jbrazio/ardufocus/.pages/assets/images/misc/homer.png

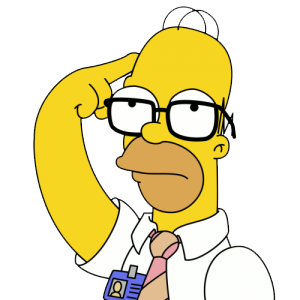
.pages/assets/images/misc/homer.png
