jbrazio/ardufocus/.pages/assets/images/pages/28byj-48-uln2003.jpg

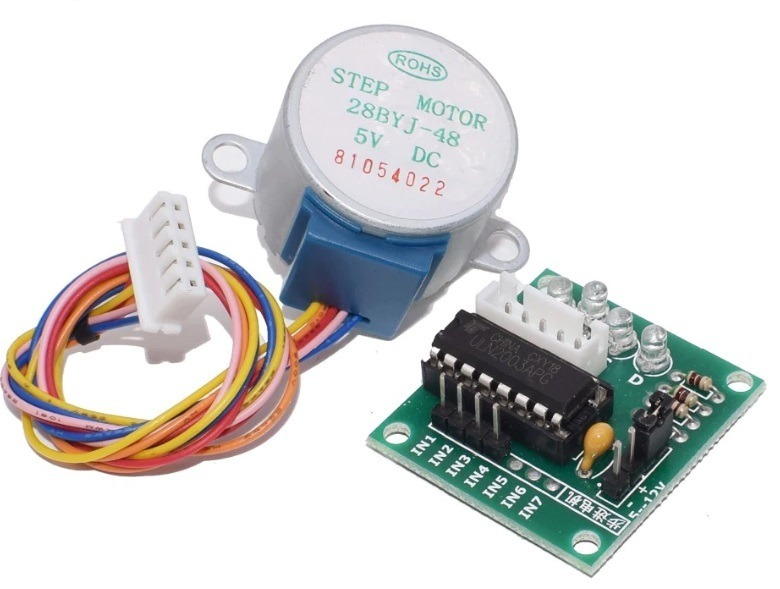
.pages/assets/images/pages/28byj-48-uln2003.jpg
