jbrazio/ardufocus/.pages/assets/images/pages/a4988-vref-resistor.jpg

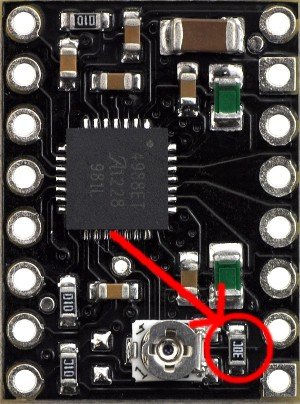
.pages/assets/images/pages/a4988-vref-resistor.jpg
