jbrazio/ardufocus/.pages/assets/images/pages/nema17.jpg

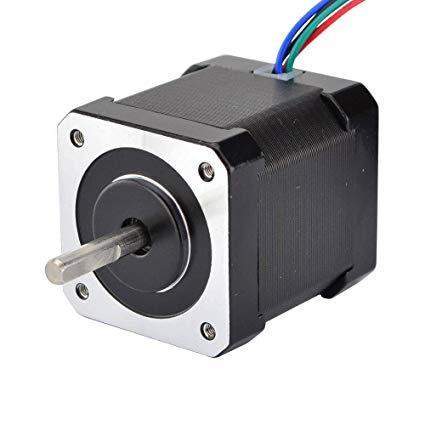
.pages/assets/images/pages/nema17.jpg
