jbrazio/ardufocus/.pages/assets/images/pages/nema-stepper-showcase.png

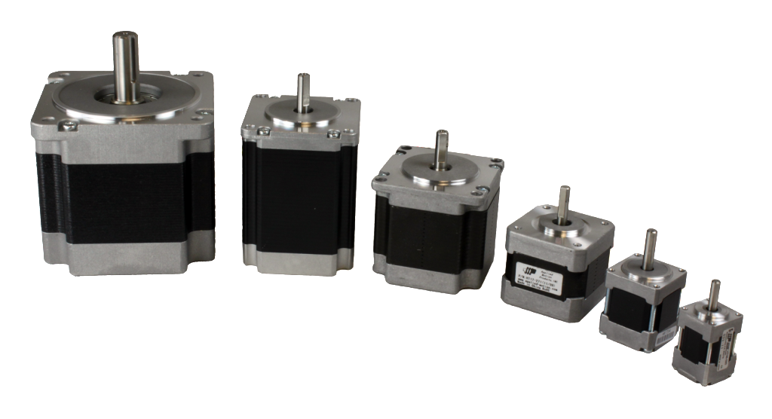
.pages/assets/images/pages/nema-stepper-showcase.png
