jbrazio/ardufocus/doc/pcb/ardufocus-bottom.png

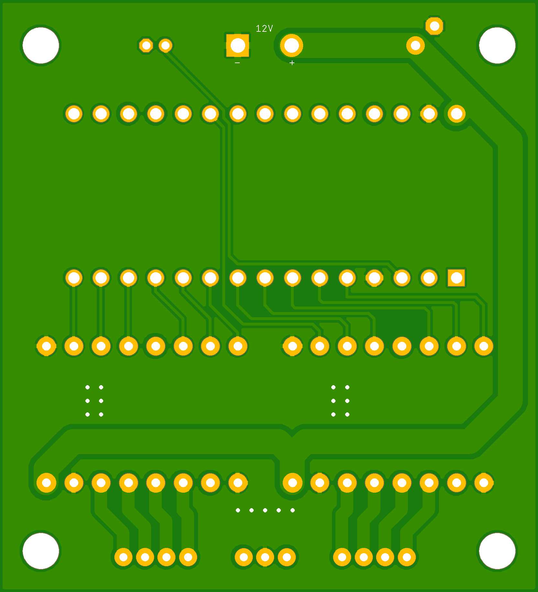
doc/pcb/ardufocus-bottom.png
