jbrazio/ardufocus/doc/pcb/ardufocus-top.png

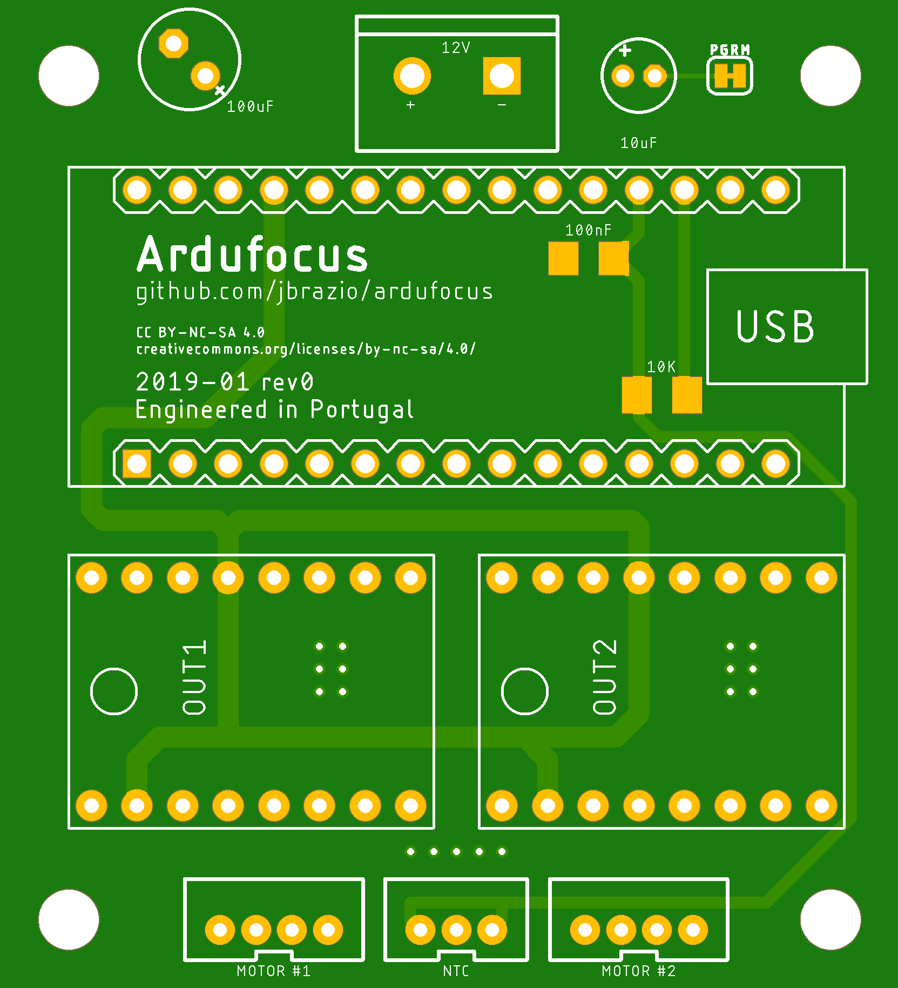
doc/pcb/ardufocus-top.png
