jbrazio/ardufocus/doc/wiki/object-focuser-box-bottom.png

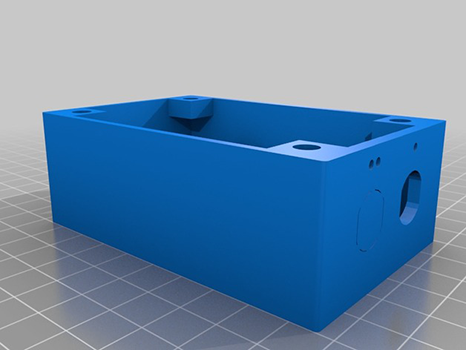
doc/wiki/object-focuser-box-bottom.png
