jbrazio/ardufocus/doc/wiki/object-focuser-box-top.png

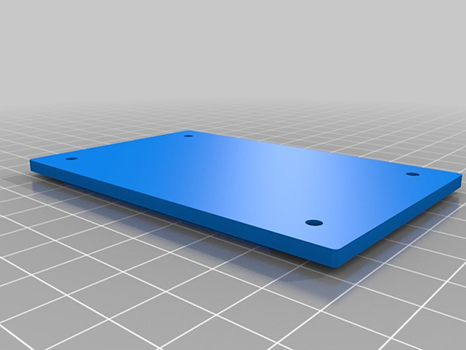
doc/wiki/object-focuser-box-top.png
