jbrazio/ardufocus/doc/wiki/object-focuser-ed80-cover.png

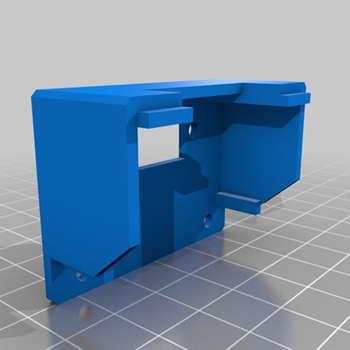
doc/wiki/object-focuser-ed80-cover.png
