jbrazio/ardufocus/doc/wiki/object-focuser-ed80-gear.png

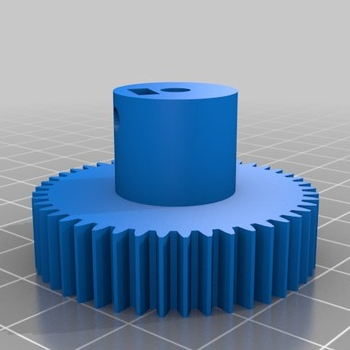
doc/wiki/object-focuser-ed80-gear.png
