jbrazio/ardufocus/doc/wiki/object-focuser-ed80-pinion.png

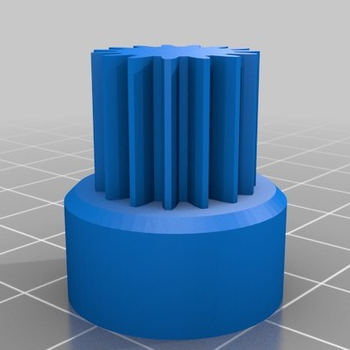
doc/wiki/object-focuser-ed80-pinion.png
