jbrazio/ardufocus/doc/wiki/object-focuser-ed80.png

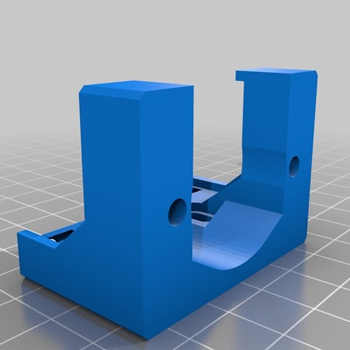
doc/wiki/object-focuser-ed80.png
