jbrazio/ardufocus/doc/wiki/sgp-focus-01.jpg

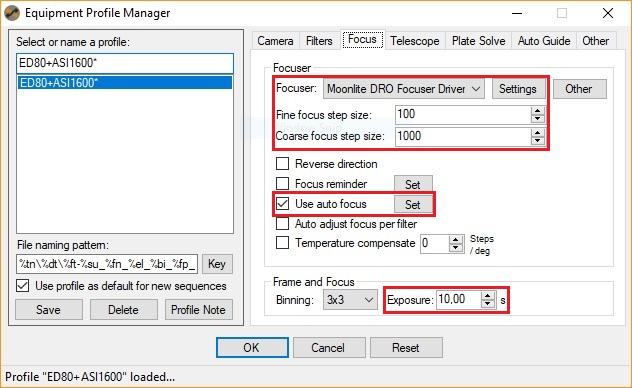
doc/wiki/sgp-focus-01.jpg
