jbrazio/ardufocus/doc/wiki/sgp-focus-02.jpg

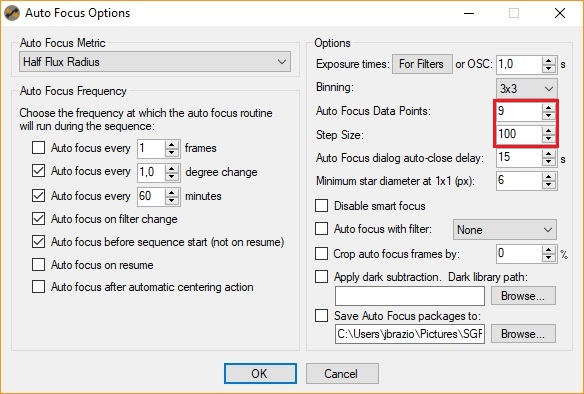
doc/wiki/sgp-focus-02.jpg
