jbrazio/ardufocus/doc/wiki/sgp-focus-03.jpg

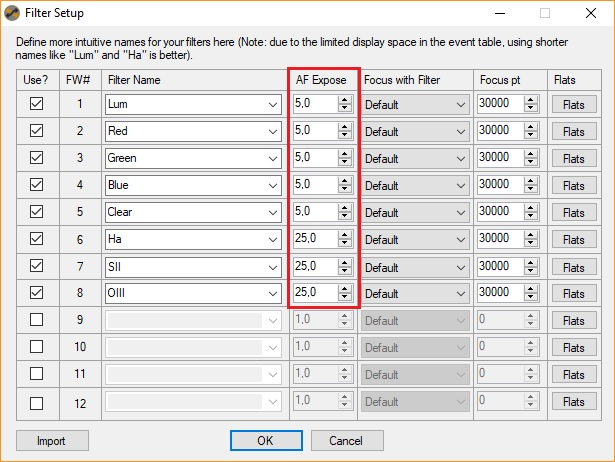
doc/wiki/sgp-focus-03.jpg
