jbrazio/ardufocus/ardufocus/isr.cpp

/**
 * Ardufocus - Moonlite compatible focuser
 * Copyright (C) 2017-2019 João Brázio [joao@brazio.org]
 *
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
 */

#include "isr.h"

/**
 * @brief Timer0 interrupt handler
 * @details
 *
 */
ISR(TIMER0_COMPA_vect)
{
  #ifdef DEBUG_ISR
    PORTB ^= bit(PB5);
  #endif

  #ifdef MOTOR1_HAS_DRIVER
    #ifdef DEBUG_ISR
      PORTC ^= bit(PC2);
    #endif

    //
    // This block takes ~50uS to execute when motor is stepping
    //

    g_motor1->tick();

    // previous motor state
    static bool pstate1 = g_motor1->is_moving();

    // current motor state
    bool cstate1 = g_motor1->is_moving();

    if(cstate1 != pstate1) {
      if(cstate1 == false) {
        g_config.position_m1 = g_motor1->get_current_position();
        g_config.speed_m1 = g_motor1->get_speed();
        g_config.half_step_m1 = (g_motor1->get_step_mode() == 0xFF);
        eeprom_save(&g_config);
      }
      pstate1 = cstate1;
    }

    #ifdef DEBUG_ISR
      PORTC ^= bit(PC2);
    #endif
  #endif

  #ifdef MOTOR2_HAS_DRIVER
    #ifdef DEBUG_ISR
      PORTC ^= bit(PC3);
    #endif

    //
    // This block takes ~50uS to execute when motor is stepping
    //
    //
    g_motor2->tick();

    // previous motor state
    static bool pstate2 = g_motor2->is_moving();

    // current motor state
    bool cstate2 = g_motor2->is_moving();

    if(cstate2 != pstate2) {
      if(cstate2 == false) {
        g_config.position_m2 = g_motor2->get_current_position();
        g_config.speed_m2 = g_motor2->get_speed();
        g_config.half_step_m2 = (g_motor2->get_step_mode() == 0xFF);
        eeprom_save(&g_config);
      }
      pstate2 = cstate2;
    }

    #ifdef DEBUG_ISR
      PORTC ^= bit(PC3);
    #endif
  #endif

  #ifdef DEBUG_ISR
    PORTB ^= bit(PB5);
  #endif
}

/**
 * @brief Timer2 interrupt handler
 * @details
 *
 */
ISR(TIMER2_COMPA_vect)
{
  static uint8_t counter = 0;

  switch(counter++)
  {
    case NTC_ADC_CHANNEL + 10:
      Analog::read_async(NTC_ADC_CHANNEL);
      break;

    #ifdef USE_UI_KAP
    case UI_KAP_ADC_CHANNEL + 30:
      Analog::read_async(UI_KAP_ADC_CHANNEL);
      break;
    #endif

    default:
      if(counter > 40) { counter = 0; }
  }
}
