jbrazio/ardufocus/ardufocus/a4988.cpp

/**
 * Ardufocus - Moonlite compatible focuser
 * Copyright (C) 2017-2019 João Brázio [joao@brazio.org]
 *
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
 */

#include "a4988.h"

/**
 * @brief [brief description]
 * @details [long description]
 *
 */
void a4988::init()
{
  stepper::init();

  IO::set_as_output(m_pinout.ms1);
  IO::set_as_output(m_pinout.ms2);
  IO::set_as_output(m_pinout.ms3);
  IO::set_as_output(m_pinout.step);
  IO::set_as_output(m_pinout.sleep);
  IO::set_as_output(m_pinout.direction);

  IO::write(m_pinout.ms1,        LOW);
  IO::write(m_pinout.ms2,        LOW);
  IO::write(m_pinout.ms3,        LOW);
  IO::write(m_pinout.step,       LOW);
  IO::write(m_pinout.direction,  LOW);

  // active low logic
  IO::write(m_pinout.sleep, (m_sleep_when_idle) ? LOW : HIGH);
}


/**
 * @brief [brief description]
 * @details [long description]
 *
 */
void a4988::halt()
{

  stepper::halt();
  m_sleep_timeout_cnt = ((m_sleep_timeout * 1000000UL) / TIMER0_TICK);
  IO::write(m_pinout.step, LOW);

  // A4988: 400ns, A8825: 1.3us
  util::delay_2us();
}


/**
 * @brief [brief description]
 * @details [long description]
 *
 */
void a4988::set_full_step()
{
  m_mode = 0x00;
  IO::write(m_pinout.ms1, LOW);
  IO::write(m_pinout.ms2, LOW);
  IO::write(m_pinout.ms3, LOW);

  // A4988: 400ns, A8825: 1.3us
  util::delay_2us();
}


/**
 * @brief [brief description]
 * @details [long description]
 *
 */
void a4988::set_half_step()
{
  m_mode = 0xFF;
  IO::write(m_pinout.ms1, HIGH);
  IO::write(m_pinout.ms2, LOW);
  IO::write(m_pinout.ms3, LOW);

  // A4988: 400ns, A8825: 1.3us
  util::delay_2us();
}


/**
 * @brief [brief description]
 * @details [long description]
 *
 */
bool a4988::step_cw()
{
  switch(IO::read(m_pinout.direction))
  {
    case LOW:
      IO::write(m_pinout.direction, HIGH);
      // A4988: 400ns, A8825: 1.3us
      util::delay_2us();

    case HIGH:
      ;

    default:
      return step();
  }
}


/**
 * @brief [brief description]
 * @details [long description]
 *
 */
bool a4988::step_ccw()
{
  switch(IO::read(m_pinout.direction))
  {
    case LOW:
      ;

    case HIGH:
      IO::write(m_pinout.direction, LOW);
      // A4988: 400ns, A8825: 1.3us
      util::delay_2us();

    default:
      return step();
  }
}


/**
 * @brief [brief description]
 * @details [long description]
 *
 */
bool a4988::step()
{
  if(m_sleep_when_idle && !IO::read(m_pinout.sleep)) {
    IO::write(m_pinout.sleep, HIGH);
    // A4988: 200ns, A8825: 1.7ms
    util::delay_2ms();
  }

  /*
   * The A4988 driver will physically step the motor when
   * transitioning from a HIGH to LOW signal, the internal
   * position counter should only be updated under this
   * condition.
   */

  // A4988: 1us, A8825: 1.9us
  IO::write(m_pinout.step, HIGH);
  util::delay_2us();

  // A4988: 1us, A8825: 1.9us
  IO::write(m_pinout.step, LOW);
  util::delay_2us();

  return true;
}


/**
 * @brief [brief description]
 * @details [long description]
 *
 */
void a4988::sleep()
{
  if(m_sleep_when_idle && m_sleep_timeout_cnt) {
    --m_sleep_timeout_cnt;

    if(!m_sleep_timeout_cnt) {
      IO::write(m_pinout.sleep, LOW);
    }
  }
}
